stefanloen/tahmo/control/src/comms.rs

use core::cmp::max;
use core::{i8, u8};

use defmt::{info, Format};
use embassy_futures::select::{select, Either};
use embassy_time::{Instant, Timer};
use embassy_sync::{blocking_mutex::raw::CriticalSectionRawMutex, channel::Channel};
use heapless::Vec;
use libm::floorf;

use crate::messages::{CommReqMsg, CommResMsg};
use crate::rockblock::{IMTMessage, RockBlock9704, BODY_SIZE, IMT_DEFAULT_TOPIC};
use crate::storage::MeasurementStorage;
use crate::types::{Event, MAX_EVENTS, MAX_SECTORS, Measurement, NUM_MEASUREMENTS, Sector};
use crate::StorageType;

const MEASUREMENT_PACKET_SIZE: usize = 10;
const PACKET_METADATA_SIZE: usize = 10;
const PACKET_MEASUREMENT_COUNT_SIZE: usize = 1;
const MAX_MEASUREMENT_PACKETS: usize = 10;
const PACKET_SIZE: usize = PACKET_METADATA_SIZE + PACKET_MEASUREMENT_COUNT_SIZE+ (MAX_MEASUREMENT_PACKETS * MEASUREMENT_PACKET_SIZE);

const MAX_STANDARD_DEVIATION: f32 = 1.0;
const MAX_RELATIVE_HEIGHT: f32 = 20.0;
const MIN_TEMPERATURE_C: f32 = -30.0;
const MAX_TEMPERATURE_C: f32 = 80.0;
const MIN_BATTERY_MV: u32 = 2000;
const MAX_BATTERY_MV: u32 = 5000;

pub struct MeasurementPacket {
    uid: u8,
    relative_height_mean: u16,
    relative_height_std: u8,
    num_observations_used: u8,
    num_observations_seen: u8,
    start_time_minutes: u16,
    end_time_minutes: u16,
}

impl MeasurementPacket {
    pub fn new(uid: u8, relative_height_mean: u16, relative_height_std: u8, num_observations_used: u8, num_observations_seen: u8, start_time_minutes: u16, end_time_minutes: u16) -> Self {
        Self {
            uid,
            relative_height_mean,
            relative_height_std,
            num_observations_used,
            num_observations_seen,
            start_time_minutes,
            end_time_minutes
        }
    }

    pub fn to_bytes(&self) -> [u8; MEASUREMENT_PACKET_SIZE] {
        let mut data = [0u8; MEASUREMENT_PACKET_SIZE];
        data[0] = self.uid;
        data[1..3].copy_from_slice(&self.relative_height_mean.to_le_bytes());
        data[3] = self.relative_height_std;
        data[4] = self.num_observations_used;
        data[5] = self.num_observations_seen;
        data[6..8].copy_from_slice(&self.start_time_minutes.to_le_bytes());
        data[8..10].copy_from_slice(&self.end_time_minutes.to_le_bytes());
        data
    }
}

pub struct Packet {
    battery: u8,
    temp: u8,
    lat: u8,
    lon: u8,
    charge_state_fraction: [u8; 4],
    bat_low: bool,
    boot_count: u8,
    measurements: Vec<MeasurementPacket, MAX_MEASUREMENT_PACKETS>,
}

impl Packet {
    pub fn new(battery: u8, temp: u8, charge_state_fraction: [u8; 4], bat_low: bool, boot_count: u8) -> Self {
        Self {
            battery,
            temp,
            lat: 0,
            lon: 0,
            charge_state_fraction,
            bat_low,
            boot_count,
            measurements: Vec::new(),
        }
    }

    pub fn set_location(&mut self, lat: u8, lon: u8) {
        self.lat = lat;
        self.lon = lon;
    }

    pub fn push(&mut self, measurement: MeasurementPacket) -> Result<(), ()> {
        self.measurements.push(measurement).map_err(|_| ())
    }

    pub fn to_bytes(&self) -> Vec<u8, PACKET_SIZE> {
        let mut data = Vec::<u8, PACKET_SIZE>::new();
        
        // Metadata
        data.push(self.battery).ok();
        data.push(self.temp).ok();
        data.push(self.lat).ok();
        data.push(self.lon).ok();
        data.extend_from_slice(&self.charge_state_fraction).ok();
        data.push(self.bat_low as u8).ok();
        data.push(self.boot_count).ok();

        // Measurements
        data.push(self.measurements.len() as u8).ok(); 
        for measurement in self.measurements.iter() {
            let meas_bytes = measurement.to_bytes();
            data.extend_from_slice(&meas_bytes).ok();
        }  
        data
    }
}

#[embassy_executor::task]
pub async fn task_comms(
    channel_req: &'static Channel<CriticalSectionRawMutex, CommReqMsg, 8>,
    channel_res: &'static Channel<CriticalSectionRawMutex, CommResMsg, 8>,
    storage: &'static StorageType,
    mut rockblock: RockBlock9704,
) {
    info!("[comm] starting");
    loop {
        info!("[comm] waiting for request...");
        let select = select(
            channel_req.receive(), 
            Timer::after_secs(u32::MAX as u64)
        ).await;
        match select {
            Either::First(request) => {
                match request {
                    CommReqMsg::Send { sectors, config, battery_mv, temp_c, charge_state_fraction, bat_low, events  } => {
                        let uids: heapless::Vec<u32, MAX_SECTORS> = sectors.iter()
                            .map(|s| s.get_uid())
                            .take(MAX_SECTORS)
                            .collect();
                        info!("[comm] starting communication for sectors {:?}", uids.as_slice());
                        let result = run_comms(
                            &mut rockblock, 
                            storage, 
                            sectors, 
                            battery_mv, 
                            temp_c,
                            charge_state_fraction,
                            bat_low,
                            events
                        ).await;
                        if result.is_err() {
                            info!("[comm] communication failed");
                            channel_res.send(CommResMsg::Fail { 
                                sector_uids: uids,
                                error: result.unwrap_err() 
                            }).await;
                        } else {
                            channel_res.send(CommResMsg::Success { 
                                sector_uids: uids,
                            }).await;
                        }
                    },
                    CommReqMsg::GetConstellationState => {
                        info!("[comm] Getting constellation state");
                        let result = get_constellation_state(&mut rockblock).await;
                        if result.is_err() {
                            info!("[comm] Getting constellation failed");
                            channel_res.send(CommResMsg::ConstellationStateFail { error: result.unwrap_err() }).await;
                        } else {
                            info!("[comm] Getting constellation success");
                            let (signal_bars_max, signal_level_max, constellation_visible) = result.unwrap();
                            channel_res.send(CommResMsg::ConstellationState { signal_bars_max, signal_level_max, constellation_visible}).await;
                        }
                    }
                }
            }
            Either::Second(_) => {}
        }
    }
}

#[derive(Debug, Format)]
pub enum CommsError {
    StorageAccess,
    RockBlockNoPower,
    RockBlockNotReady,
    RockBlockSendFail,
}

async fn run_comms(
    rockblock: &mut RockBlock9704,
    storage: &'static StorageType,
    sectors: Vec<Sector, MAX_SECTORS>,
    battery_mv: Option<u32>,
    temp_c: Option<f32>,
    charge_state_fraction: [u8; 4],
    bat_low: bool,
    events: Vec<Event, MAX_EVENTS>
) -> Result<(), CommsError> {
    info!("[comm] Turning on RockBlock");
    rockblock.power_on().await;
    if rockblock.status != crate::rockblock::RockBlock9704Status::Unchecked {
        info!("[comm] RockBlock not ready to be checked, aborting comms and powering off");
        rockblock.power_off().await;
        info!("[comm] RockBlock powered off");
        return Err(CommsError::RockBlockNoPower);
    }
    info!("[comm] Checking RockBlock status");
    rockblock.check_status().await;
    if rockblock.status != crate::rockblock::RockBlock9704Status::Ready {
        info!("[comm] RockBlock not ready, aborting comms");
        info!("[comm] Turning off RockBlock");
        rockblock.power_off().await;
        info!("[comm] RockBlock powered off");
        return Err(CommsError::RockBlockNotReady);
    }
    info!("[comm] RockBlock ready, preparing packet");

    let scaled_bat_mv = match battery_mv {
        Some(mv) => u32_to_u8(mv, MIN_BATTERY_MV, MAX_BATTERY_MV),
        None => 0
    }; 

    let scaled_temp_c = match temp_c {
        Some(c) => f32_to_u8(c, MIN_TEMPERATURE_C, MAX_TEMPERATURE_C),
        None => 0
    }; 

    let boot_count = events
        .iter()
        .filter(|e| matches!(e, Event::Boot(_)))
        .count() as u8;

    let mut packet = Packet::new(
        scaled_bat_mv,
        scaled_temp_c,
        charge_state_fraction,
        bat_low,
        boot_count
    );

    let mut highest_uid = 0;
    let mut lat = 0f32;
    let mut lon = 0f32;

    for sector in sectors.iter() {
        if let Ok(measurement) = get_measurement_packet(storage, sector.get_measurement_index()).await {
            if sector.get_uid() > highest_uid {
                highest_uid = sector.get_uid();
                lat = sector.get_lat();
                lon = sector.get_lon();
            }
            if packet.push(measurement).is_err() {
                info!("[comm] Packet full, stopping adding measurements");
                break;
            }
        }
    }

    packet.set_location(
        coord_to_u8(lat, 1000.0),
        coord_to_u8(lon, 1000.0)
    );

    let data = packet.to_bytes();
    info!("[comm] Sending packet with {} measurements, total size {} bytes", packet.measurements.len(), data.len());
    
    let start = Instant::now();
    let mut body = [0u8; BODY_SIZE];
    let data_slice = data.as_slice();
    let len = data_slice.len().min(BODY_SIZE);
    body[..len].copy_from_slice(&data_slice[..len]);

    let message = IMTMessage::new(
        IMT_DEFAULT_TOPIC,
        body,
        len as u8,
    );

    info!("[comm] Checking constellation");
    for _ in 0..5 {
        if let Some(result) = rockblock.get_constellation_state().await {
            info!("[comm] Constellation state: {} {} {}", result.signal_bars, result.signal_level, result.constellation_visible);
        } else {
            info!("[comm] Failed to get constellation state");
        }
        Timer::after_secs(3).await;
    }

    let result = rockblock.send_message(message).await;
    let is_error = result.is_err();
    if let Err(err) = result {
        info!("[comm] RockBlock send failed {} after {} ms", &err, (Instant::now() - start).as_millis());
    } else {
        info!("[comm] Packet sent in {} ms", (Instant::now() - start).as_millis());
    }

    info!("[comm] Turning off RockBlock");
    rockblock.power_off().await;
    info!("[comm] RockBlock powered off");

    if is_error {
        Err(CommsError::RockBlockSendFail)
    } else {
        Ok(())
    }
}

async fn get_constellation_state(rockblock: &mut RockBlock9704) -> Result<(u8, i8, bool), CommsError> {
    info!("[comm] Turning on RockBlock");
    rockblock.power_on().await;
    if rockblock.status != crate::rockblock::RockBlock9704Status::Unchecked {
        info!("[comm] RockBlock not ready to be checked, aborting comms and powering off");
        rockblock.power_off().await;
        info!("[comm] RockBlock powered off");
        return Err(CommsError::RockBlockNoPower);
    }
    info!("[comm] Checking RockBlock status");
    rockblock.check_status().await;
    if rockblock.status != crate::rockblock::RockBlock9704Status::Ready {
        info!("[comm] RockBlock not ready, aborting comms");
        info!("[comm] Turning off RockBlock");
        rockblock.power_off().await;
        info!("[comm] RockBlock powered off");
        return Err(CommsError::RockBlockNotReady);
    };

    info!("[comm] Checking constellation");
    let mut signal_bars_max: u8 = u8::MIN;
    let mut signal_level_max: i8 = i8::MIN;
    let mut constellation_visible: bool = false;

    let mut is_error = false;
    for _ in 0..5 {
        if let Some(result) = rockblock.get_constellation_state().await {
            info!("[comm] Constellation state: {} {} {}", result.signal_bars, result.signal_level, result.constellation_visible);
            signal_bars_max = max(signal_bars_max, result.signal_bars);
            signal_level_max = max(signal_level_max, result.signal_level.unwrap_or(i8::MIN));
            constellation_visible |= result.constellation_visible;
        } else {
            is_error = true;
            info!("[comm] Failed to get constellation state");
        }
        Timer::after_secs(3).await;
    }
    info!("[comm] Turning off RockBlock");
    rockblock.power_off().await;
    info!("[comm] RockBlock powered off");

    if is_error {
        Err(CommsError::RockBlockSendFail)
    } else {
        Ok((signal_bars_max, signal_level_max, constellation_visible))
    }
}

async fn get_measurement_packet(storage: &'static StorageType, measurement_index: u32) -> Result<MeasurementPacket, CommsError> {
    let measurement_storage = MeasurementStorage::new();
    let measurement: Option<Measurement>;
    {
        let mut storage_lock = storage.lock().await;
        let storage = storage_lock.as_mut().ok_or(CommsError::StorageAccess)?;
        measurement = measurement_storage.read(storage, measurement_index);
    }
    if measurement.is_none() {
        info!("[comm] Failed to get measurement {}, skipping", measurement_index);
        return Err(CommsError::StorageAccess);
    }
    let measurement = measurement.unwrap();
    let packet_measurement = MeasurementPacket::new(
        (measurement.uid % 256) as u8,
        mean_f32_to_u16(measurement.mean, MAX_RELATIVE_HEIGHT),
        f32_to_u8(measurement.std, 0.0, MAX_STANDARD_DEVIATION),
        measurement.observations.len() as u8,
        measurement.num_seen as u8,
        (measurement.start_time / 60) as u16,
        (measurement.end_time / 60) as u16,

    );
    info!(
        "[comm] Read measurement {} (with {} observations, mean {}, std {})", 
        measurement_index,
        packet_measurement.num_observations_used,
        packet_measurement.relative_height_mean,
        packet_measurement.relative_height_std
    );
    Ok(packet_measurement)
}

fn mean_f32_to_u16(value: f32, max: f32) -> u16 {
    if value < 0.0 {
        return 0;
    }
    if value > max {
        return u16::MAX;
    }
    let scaled = (value / max) * (65_535.0);
    scaled as u16
}

pub fn f32_to_u8(value: f32, min: f32, max: f32) -> u8 {
    if value <= min {
        return 0;
    }
    if value >= max {
        return 255;
    }
    let scaled = ((value - min) / (max - min)) * 255.0;
    (scaled + 0.5) as u8
}

pub fn u32_to_u8(value: u32, min: u32, max: u32) -> u8 {
    if value <= min {
        return 0;
    }
    if value >= max {
        return 255;
    }

    let scaled = ((value - min) as f32 / (max - min) as f32) * 255.0;

    (scaled + 0.5) as u8
}


fn coord_to_u8(value: f32, scale: f32) -> u8 {
    let i = (value * scale) - floorf(value * scale);

    (i * 255.0) as u8
}
